RedaMohssine/E-Wslni-Autonomous-Guide-Robot/SolidWorks CAD/assem_moteur_roue.SLDASM

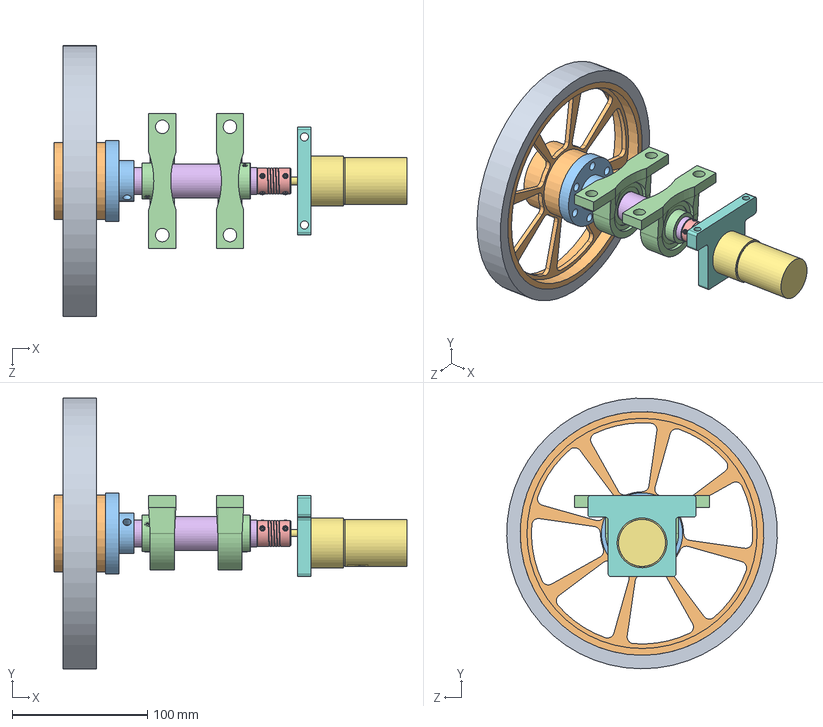
[picture p13: CAD file, 2026-05-02]
SolidWorks CAD/assem_moteur_roue.SLDASM
260.8 x 199.9 x 199.9 mm
fourche en T
moteur
arbre
Stepper Motor Flexible Coupling 6,35 x 8 mm
palier x 2
accouplement
