RedaMohssine/E-Wslni-Autonomous-Guide-Robot/SolidWorks CAD/Part1.SLDPRT

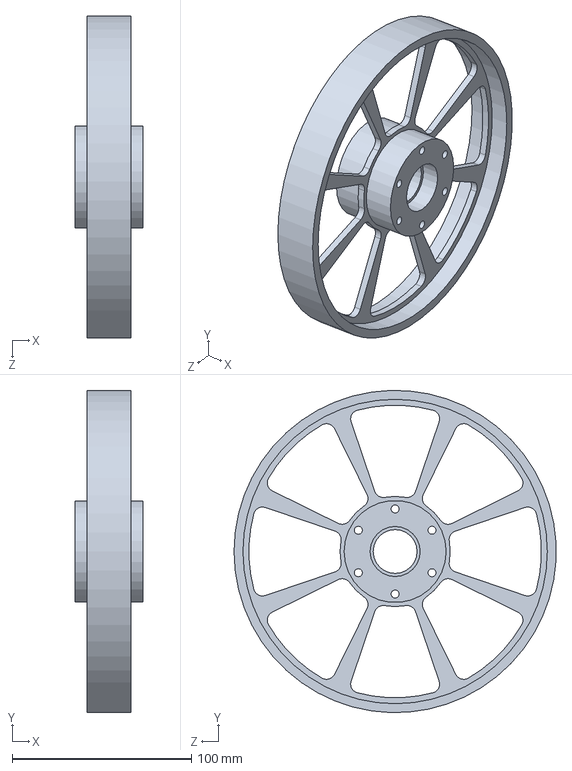
[picture p21: CAD file, 2026-05-02]
SolidWorks CAD/Part1.SLDPRT
38.0 x 179.9 x 179.8 mm
