RedaMohssine/E-Wslni-Autonomous-Guide-Robot/SolidWorks CAD/port male new.SLDPRT

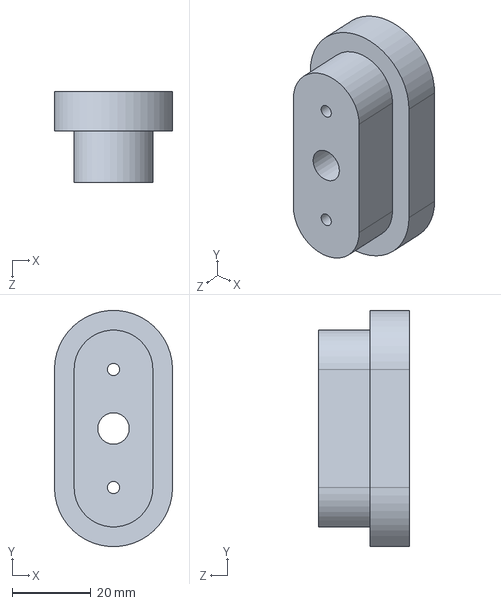
[picture p24: CAD file, 2026-05-02]
SolidWorks CAD/port male new.SLDPRT
30.0 x 59.9 x 23.0 mm
