RedaMohssine/E-Wslni-Autonomous-Guide-Robot/SolidWorks CAD/support  charge.SLDPRT

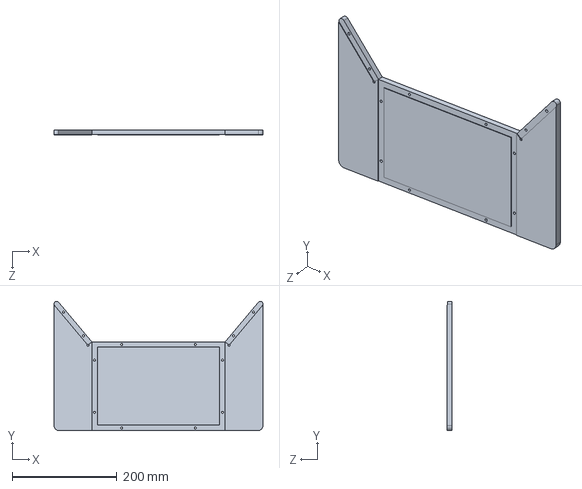
[picture p25: CAD file, 2026-05-02]
SolidWorks CAD/support charge.SLDPRT
400.0 x 247.6 x 10.0 mm
