RedaMohssine/E-Wslni-Autonomous-Guide-Robot/SolidWorks CAD/habillage_port_piece.SLDPRT

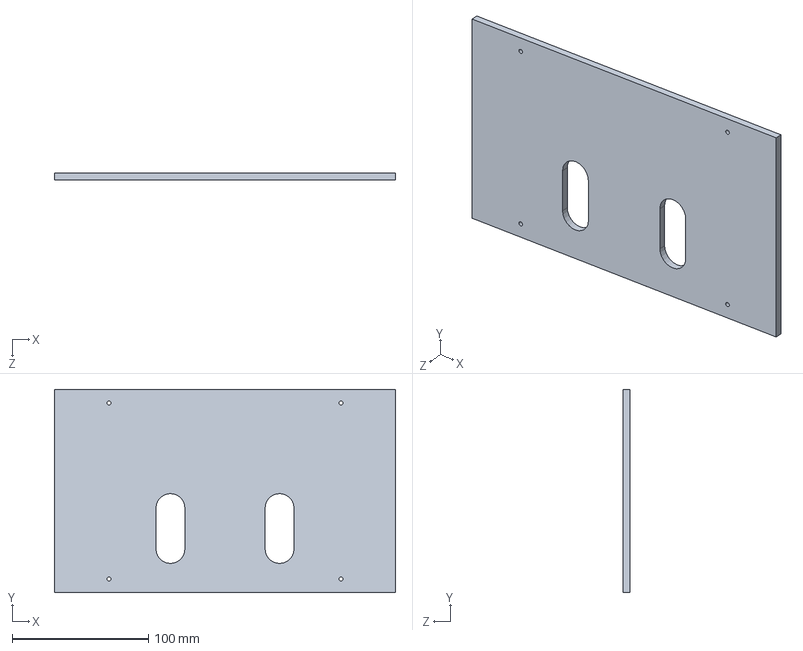
[picture p26: CAD file, 2026-05-02]
SolidWorks CAD/habillage_port_piece.SLDPRT
250.0 x 149.0 x 5.00 mm
