RedaMohssine/E-Wslni-Autonomous-Guide-Robot/SolidWorks CAD/roof.SLDPRT

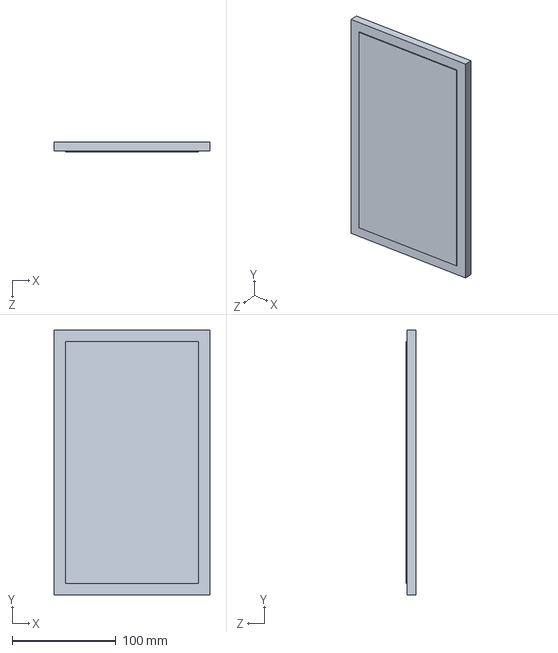
[picture p27: CAD file, 2026-05-02]
SolidWorks CAD/roof.SLDPRT
150.0 x 255.0 x 10.0 mm
