RedaMohssine/E-Wslni-Autonomous-Guide-Robot/SolidWorks CAD/lateral.SLDPRT

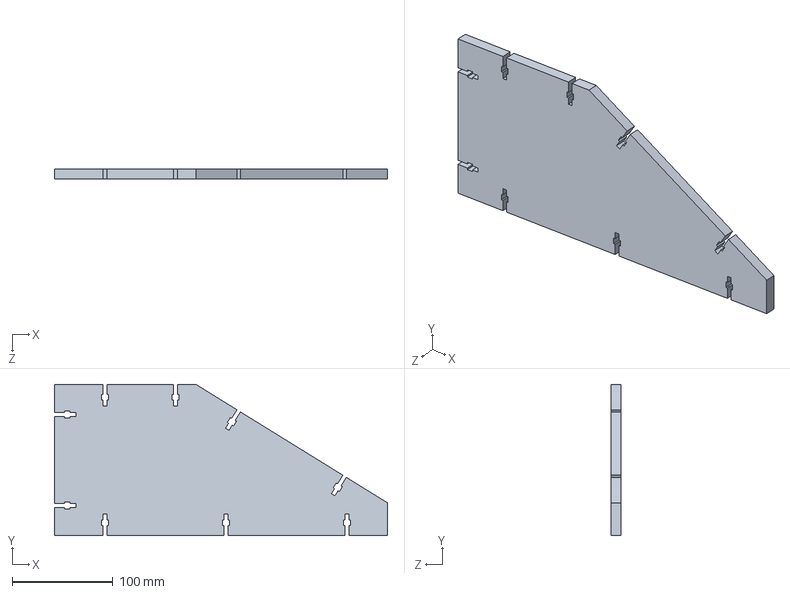
[picture p28: CAD file, 2026-05-02]
SolidWorks CAD/lateral.SLDPRT
330.0 x 150.0 x 10.0 mm
