RedaMohssine/E-Wslni-Autonomous-Guide-Robot/SolidWorks CAD/plateau4.SLDPRT

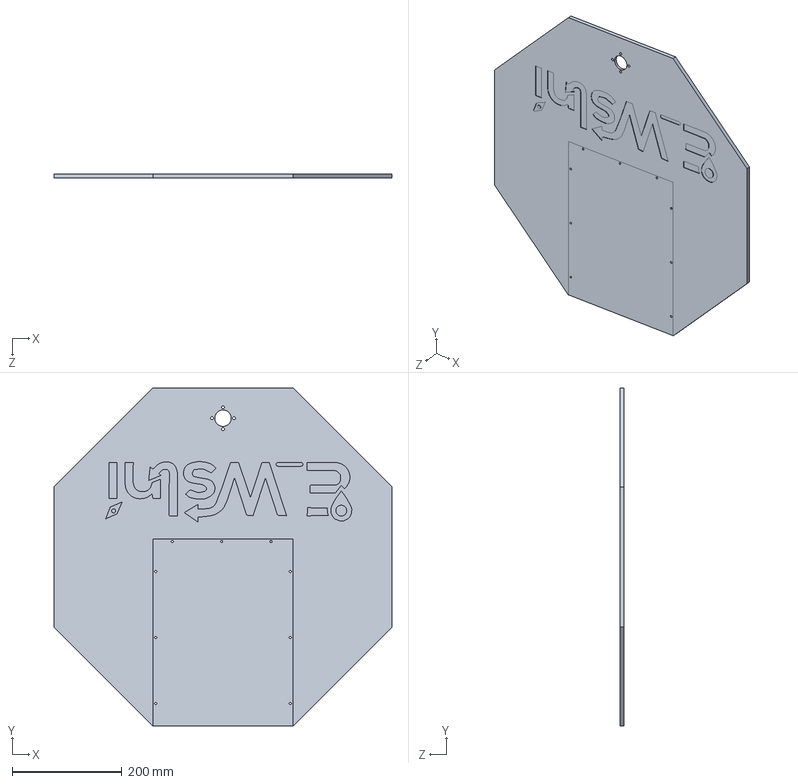
[picture p29: CAD file, 2026-05-02]
SolidWorks CAD/plateau4.SLDPRT
615.6 x 615.6 x 8.00 mm
