RedaMohssine/E-Wslni-Autonomous-Guide-Robot/SolidWorks CAD/paroi direction 1.SLDPRT

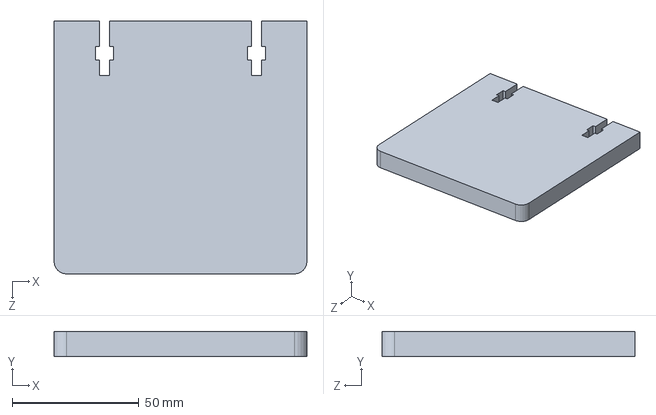
[picture p31: CAD file, 2026-05-02]
SolidWorks CAD/paroi direction 1.SLDPRT
100.0 x 10.0 x 100.0 mm
