RedaMohssine/E-Wslni-Autonomous-Guide-Robot/SolidWorks CAD/mount_bottom.SLDPRT

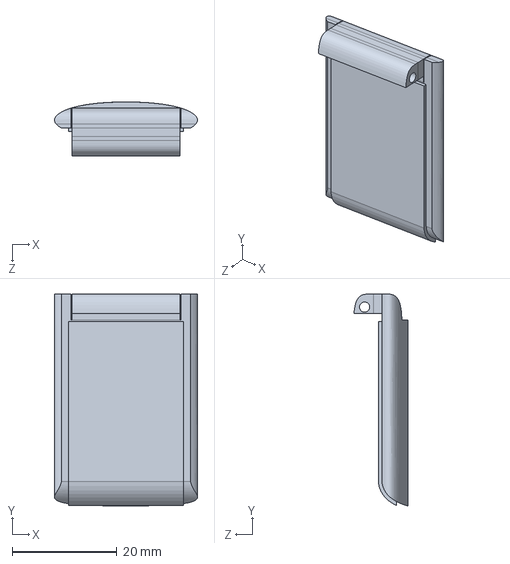
[picture p32: CAD file, 2026-05-02]
SolidWorks CAD/mount_bottom.SLDPRT
27.3 x 40.5 x 10.4 mm
