RedaMohssine/E-Wslni-Autonomous-Guide-Robot/SolidWorks CAD/RUBBER WHEEL (2.5inch).SLDPRT

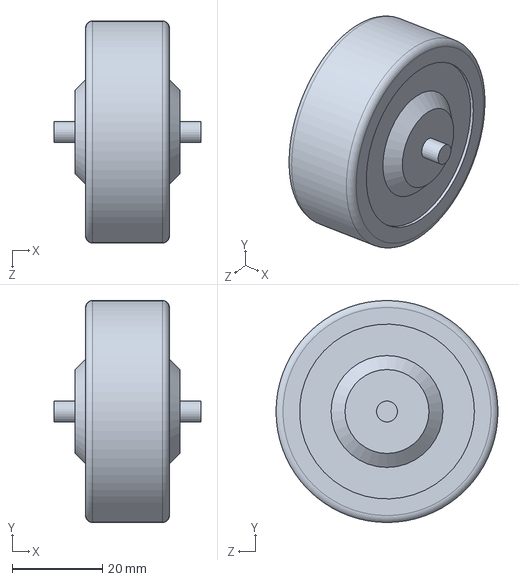
[picture p33: CAD file, 2026-05-02]
SolidWorks CAD/RUBBER WHEEL (2.5inch).SLDPRT
32.6 x 49.3 x 49.3 mm
