RedaMohssine/E-Wslni-Autonomous-Guide-Robot/SolidWorks CAD/supp_moteur.SLDPRT

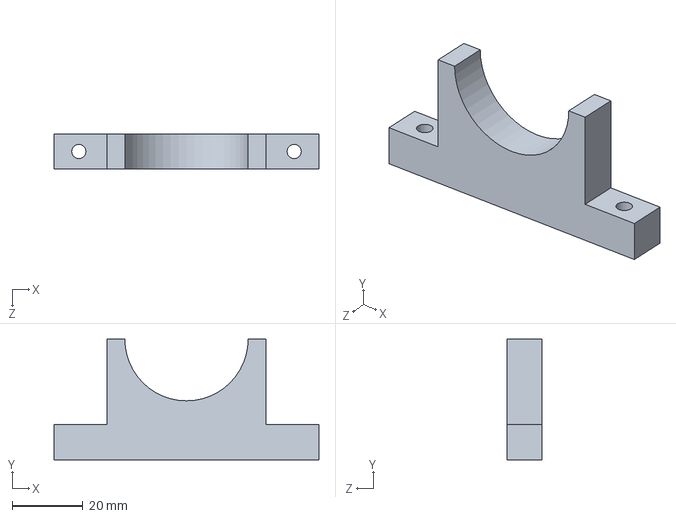
[picture p34: CAD file, 2026-05-02]
SolidWorks CAD/supp_moteur.SLDPRT
74.8 x 34.2 x 10.0 mm
