RedaMohssine/E-Wslni-Autonomous-Guide-Robot/SolidWorks CAD/CASTER WHEEL BASE LOCK.SLDPRT

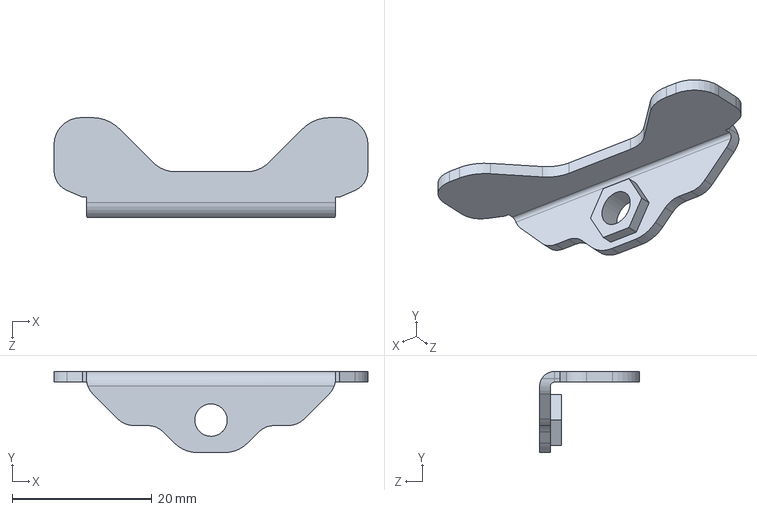
[picture p35: CAD file, 2026-05-02]
SolidWorks CAD/CASTER WHEEL BASE LOCK.SLDPRT
45.0 x 11.6 x 14.3 mm
