RedaMohssine/E-Wslni-Autonomous-Guide-Robot/SolidWorks CAD/Arduino Mega 2560.step

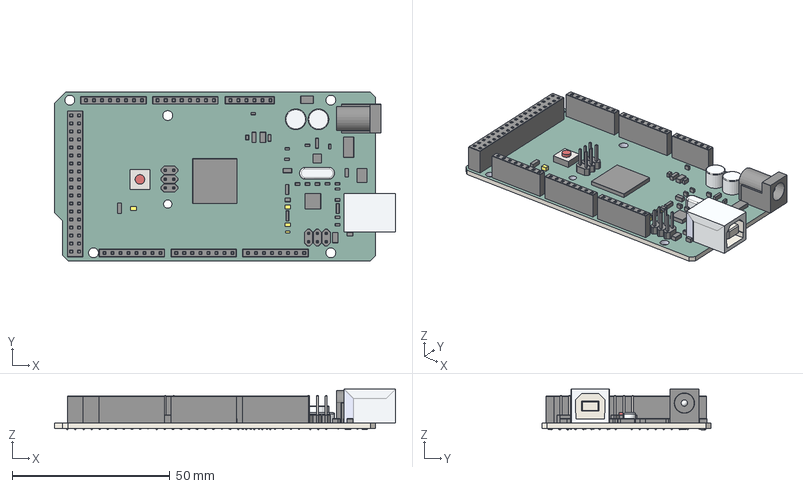
[picture p36: CAD file, 2026-05-02]
SolidWorks CAD/Arduino Mega 2560.step
107.9 x 53.4 x 13.0 mm
