RedaMohssine/E-Wslni-Autonomous-Guide-Robot/SolidWorks CAD/SD161.SLDPRT

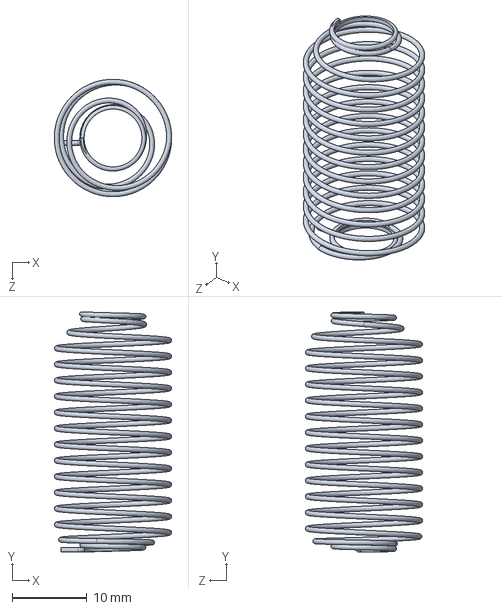
[picture p37: CAD file, 2026-05-02]
SolidWorks CAD/SD161.SLDPRT
15.7 x 32.1 x 15.7 mm
