RedaMohssine/E-Wslni-Autonomous-Guide-Robot/SolidWorks CAD/arbre.SLDPRT

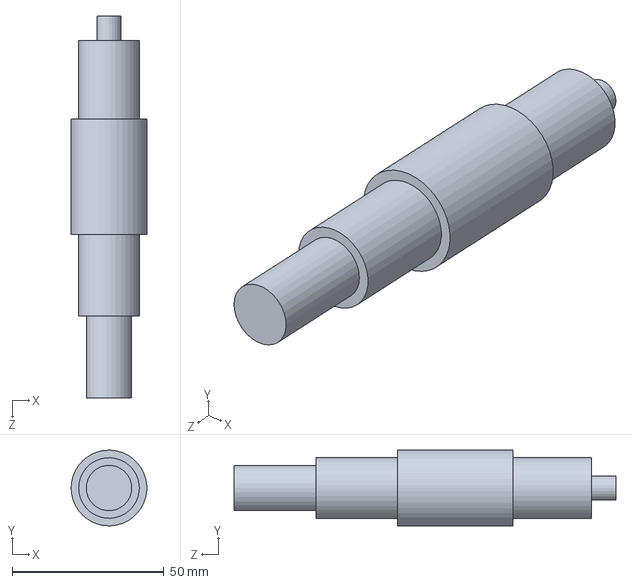
[picture p38: CAD file, 2026-05-02]
SolidWorks CAD/arbre.SLDPRT
25.0 x 25.0 x 126.0 mm
