RedaMohssine/E-Wslni-Autonomous-Guide-Robot/SolidWorks CAD/m920.step

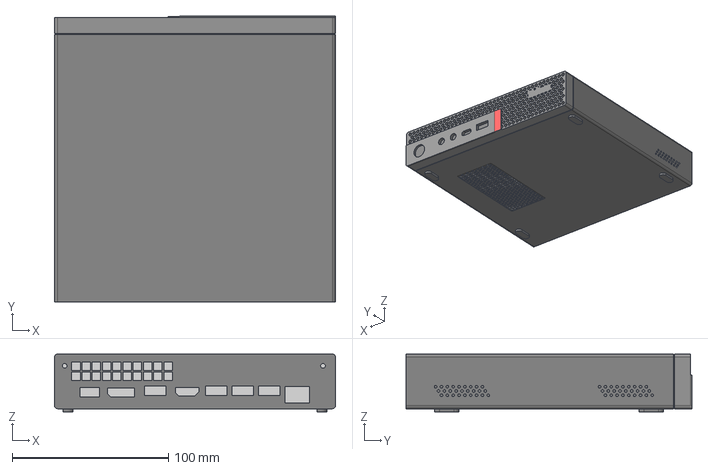
[picture p39: CAD file, 2026-05-02]
SolidWorks CAD/m920.step
180.0 x 183.0 x 37.0 mm
