RedaMohssine/E-Wslni-Autonomous-Guide-Robot/SolidWorks CAD/Port_male.SLDPRT

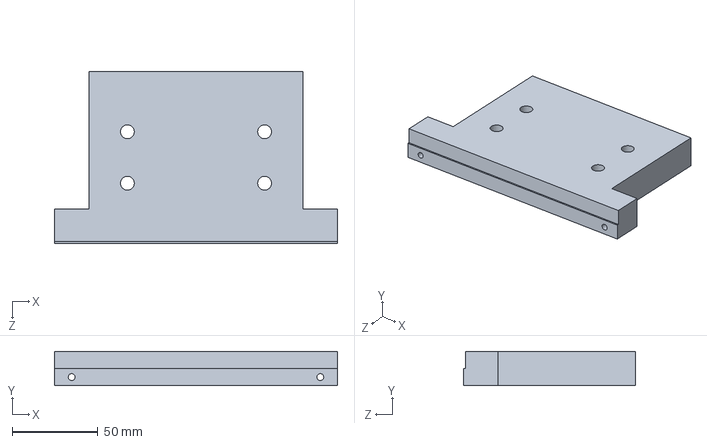
[picture p40: CAD file, 2026-05-02]
SolidWorks CAD/Port_male.SLDPRT
165.0 x 20.0 x 100.0 mm
