RedaMohssine/E-Wslni-Autonomous-Guide-Robot/SolidWorks CAD/front.SLDPRT

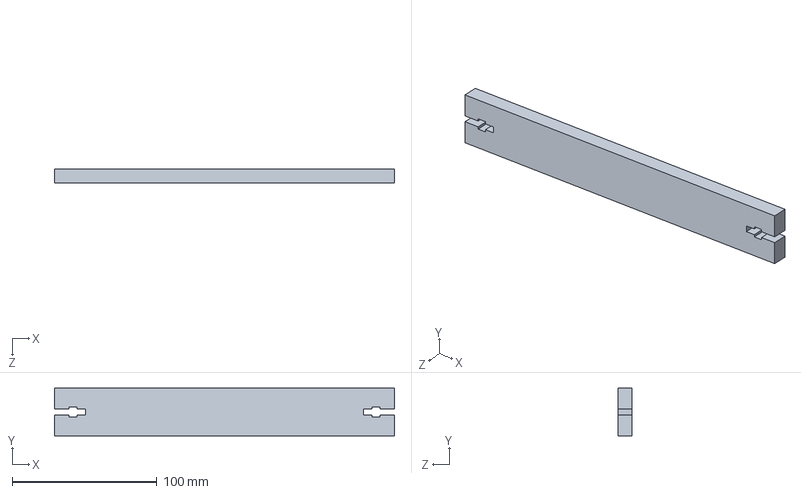
[picture p41: CAD file, 2026-05-02]
SolidWorks CAD/front.SLDPRT
235.0 x 33.0 x 10.0 mm
