RedaMohssine/E-Wslni-Autonomous-Guide-Robot/SolidWorks CAD/Stepper Motor Flexible Coupling 6,35 x 8 mm.SLDPRT

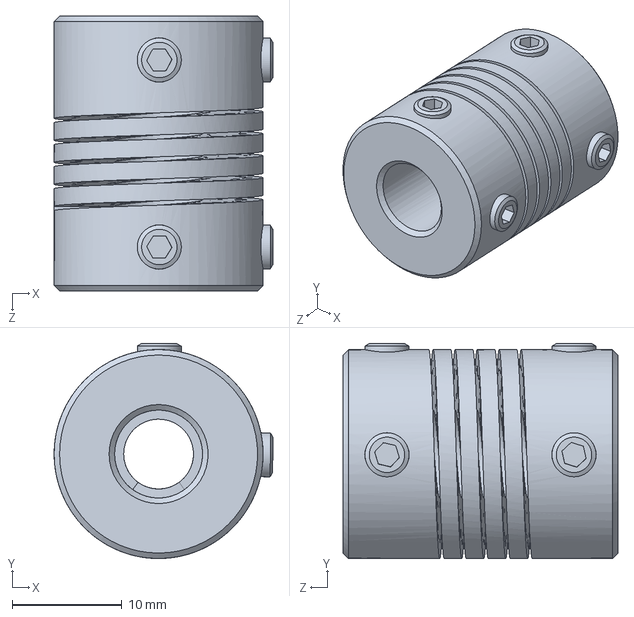
[picture p42: CAD file, 2026-05-02]
SolidWorks CAD/Stepper Motor Flexible Coupling 6,35 x 8 mm.SLDPRT
19.9 x 19.6 x 25.0 mm
