RedaMohssine/E-Wslni-Autonomous-Guide-Robot/SolidWorks CAD/Part2.SLDPRT

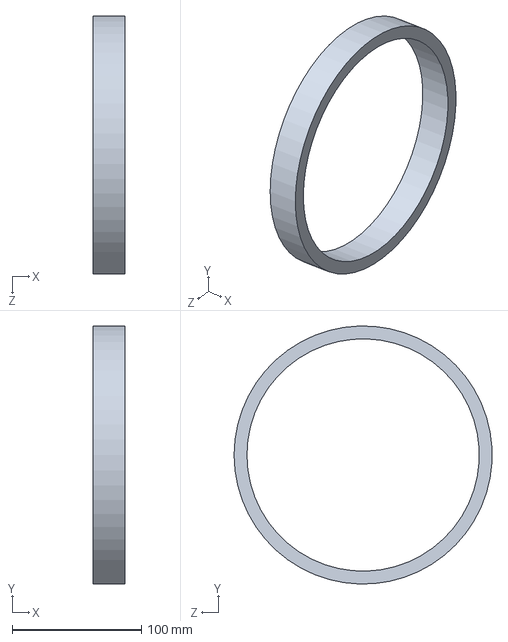
[picture p43: CAD file, 2026-05-02]
SolidWorks CAD/Part2.SLDPRT
24.5 x 199.9 x 199.8 mm
