RedaMohssine/E-Wslni-Autonomous-Guide-Robot/SolidWorks CAD/base.SLDPRT

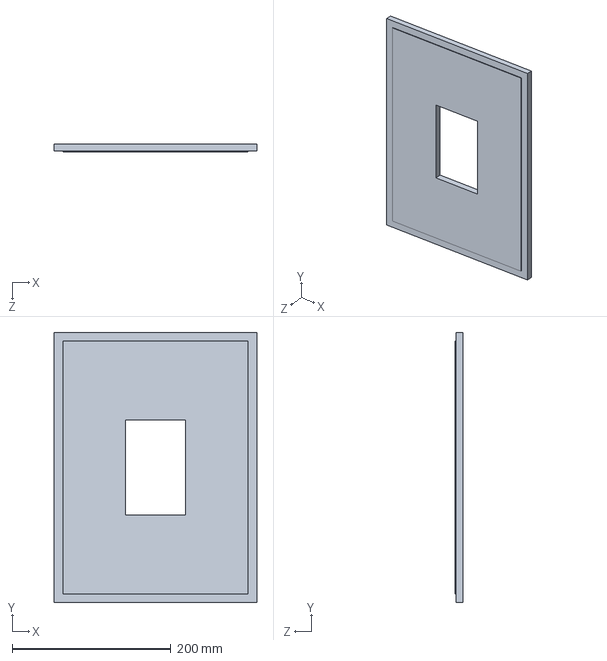
[picture p44: CAD file, 2026-05-02]
SolidWorks CAD/base.SLDPRT
255.0 x 340.0 x 10.0 mm
