RedaMohssine/E-Wslni-Autonomous-Guide-Robot/SolidWorks CAD/Vis_guide.SLDPRT

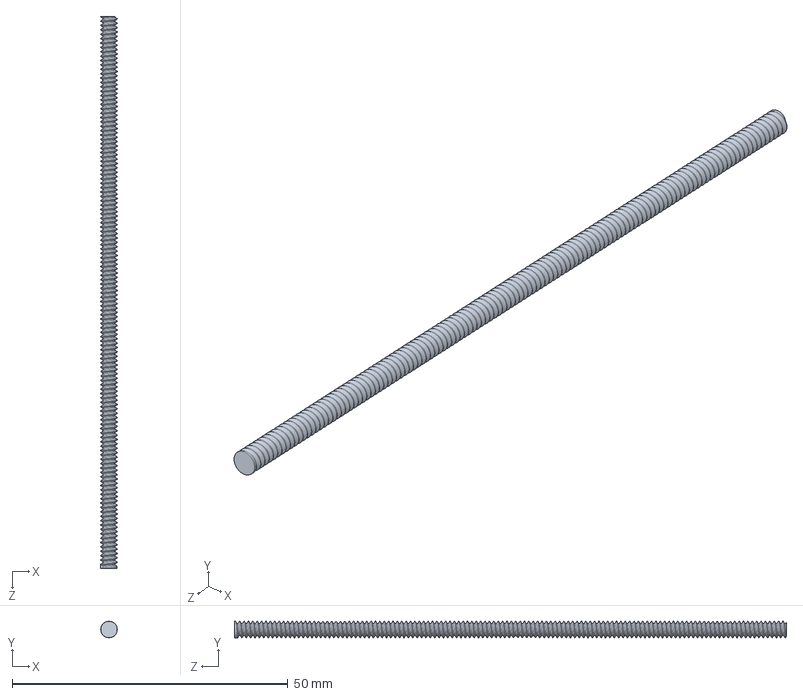
[picture p45: CAD file, 2026-05-02]
SolidWorks CAD/Vis_guide.SLDPRT
3.00 x 3.00 x 100.0 mm
