RedaMohssine/E-Wslni-Autonomous-Guide-Robot/SolidWorks CAD/plateau3.SLDPRT

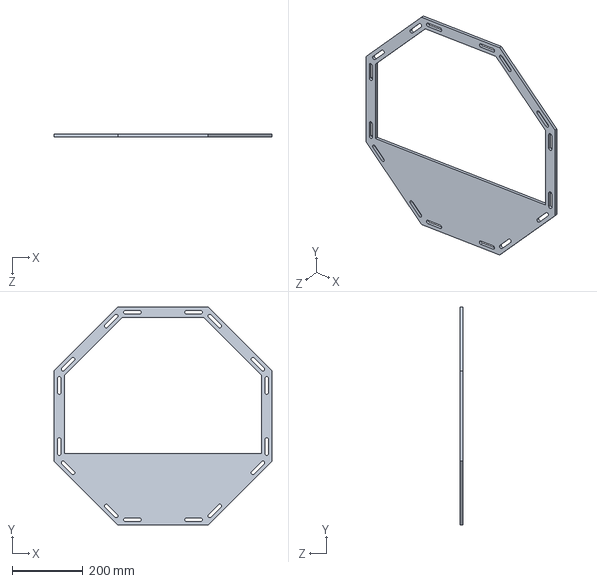
[picture p46: CAD file, 2026-05-02]
SolidWorks CAD/plateau3.SLDPRT
615.6 x 615.6 x 8.00 mm
