RedaMohssine/E-Wslni-Autonomous-Guide-Robot/SolidWorks CAD/palier.SLDPRT

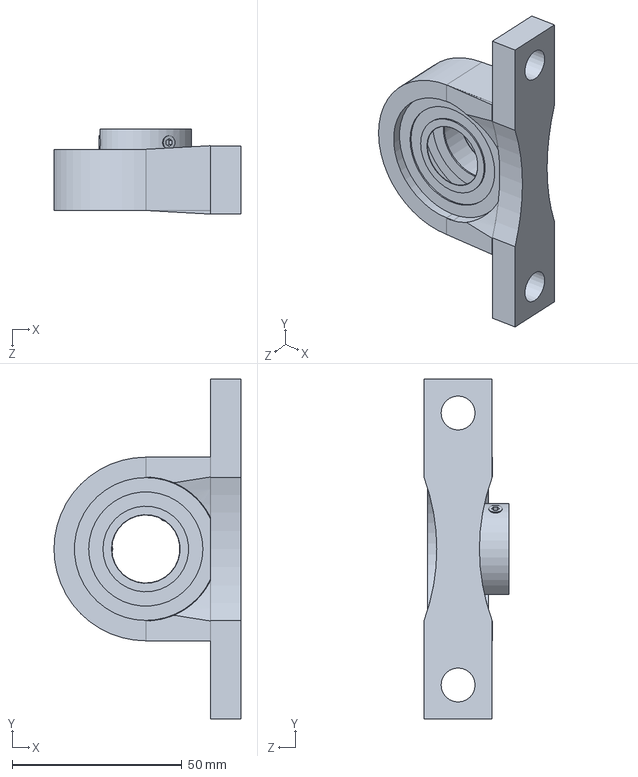
[picture p47: CAD file, 2026-05-02]
SolidWorks CAD/palier.SLDPRT
55.0 x 100.0 x 25.1 mm
