RedaMohssine/E-Wslni-Autonomous-Guide-Robot/SolidWorks CAD/back.SLDPRT

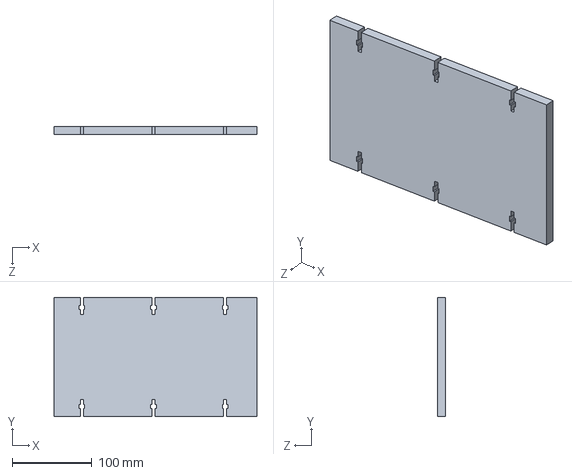
[picture p48: CAD file, 2026-05-02]
SolidWorks CAD/back.SLDPRT
255.0 x 150.0 x 10.0 mm
