RedaMohssine/E-Wslni-Autonomous-Guide-Robot/SolidWorks CAD/batterie_Turnigy.SLDPRT

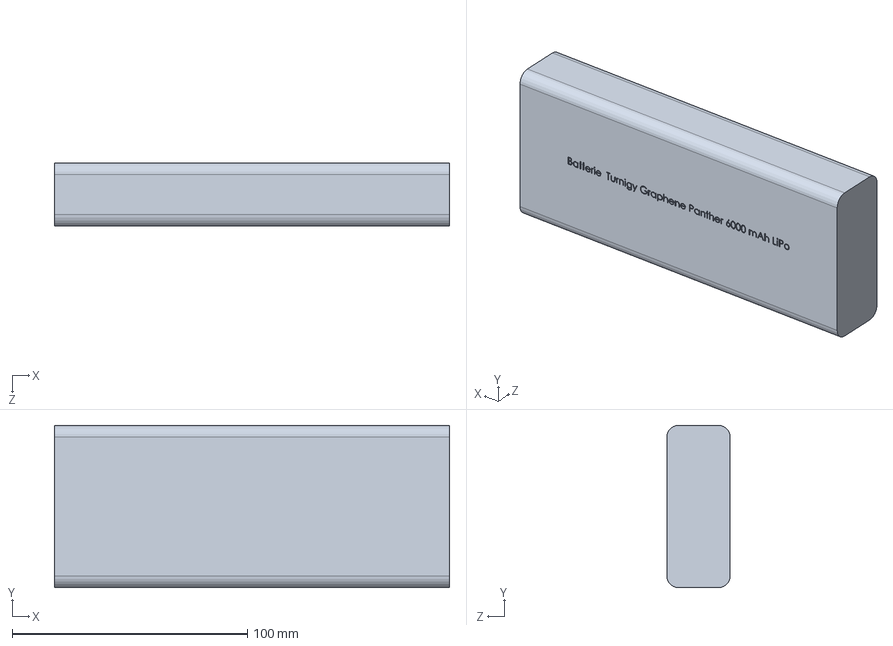
[picture p49: CAD file, 2026-05-02]
SolidWorks CAD/batterie_Turnigy.SLDPRT
168.0 x 69.0 x 27.0 mm
