RedaMohssine/E-Wslni-Autonomous-Guide-Robot/SolidWorks CAD/moteur.SLDPRT

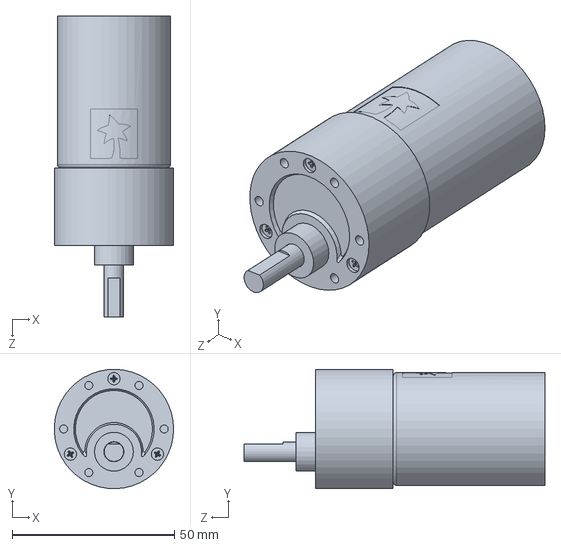
[picture p50: CAD file, 2026-05-02]
SolidWorks CAD/moteur.SLDPRT
36.8 x 36.8 x 92.8 mm
