RedaMohssine/E-Wslni-Autonomous-Guide-Robot/SolidWorks CAD/chassis_v2.SLDPRT

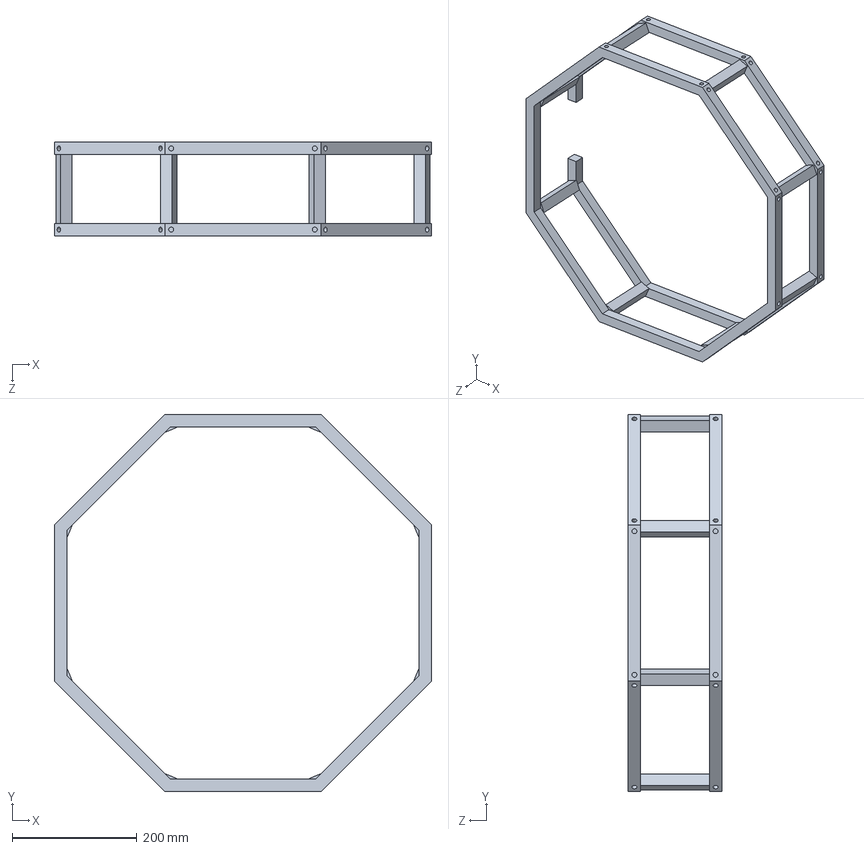
[picture p51: CAD file, 2026-05-02]
SolidWorks CAD/chassis_v2.SLDPRT
603.6 x 603.6 x 150.0 mm
