RedaMohssine/E-Wslni-Autonomous-Guide-Robot/SolidWorks CAD/fourche en T.SLDPRT

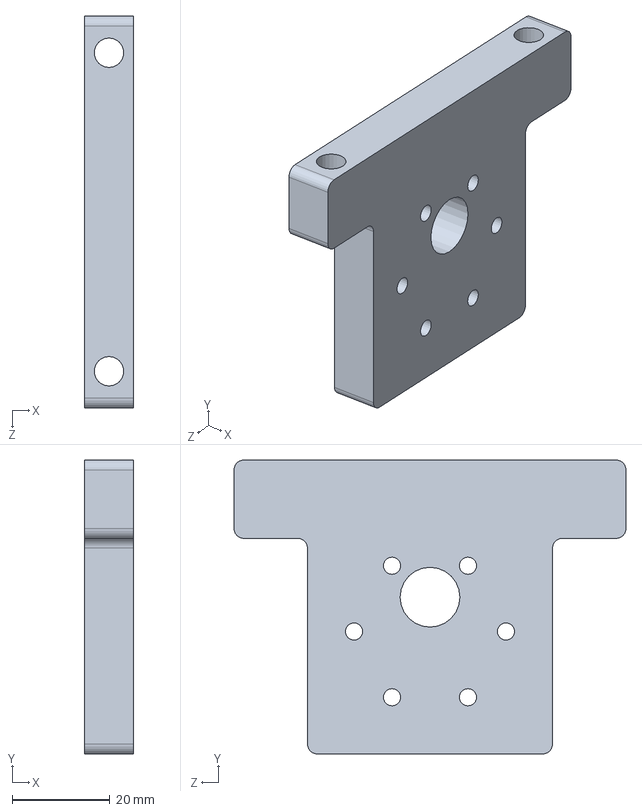
[picture p52: CAD file, 2026-05-02]
SolidWorks CAD/fourche en T.SLDPRT
10.0 x 60.0 x 80.0 mm
