RedaMohssine/E-Wslni-Autonomous-Guide-Robot/SolidWorks CAD/CASTER WHEEL BASE.SLDPRT

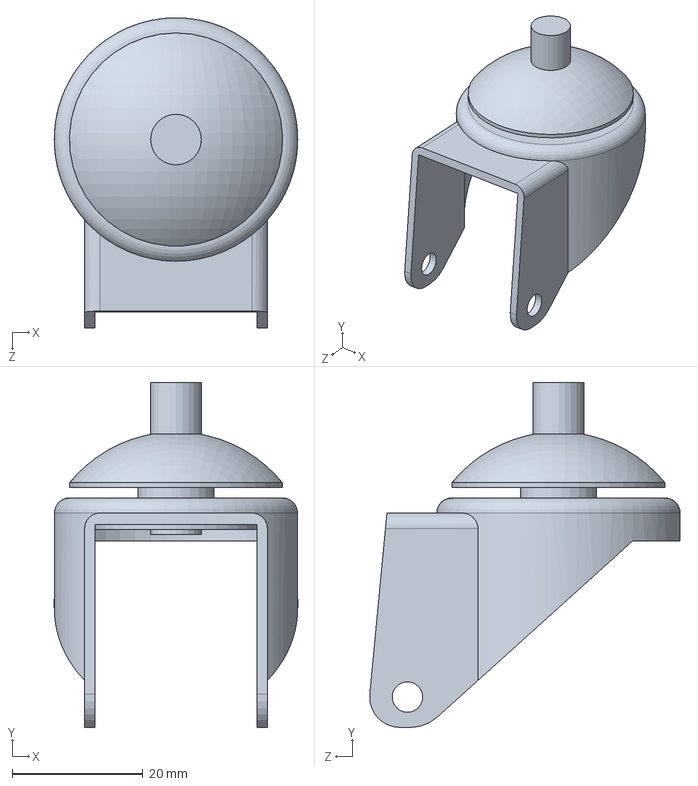
[picture p53: CAD file, 2026-05-02]
SolidWorks CAD/CASTER WHEEL BASE.SLDPRT
37.3 x 52.8 x 47.5 mm
