RedaMohssine/E-Wslni-Autonomous-Guide-Robot/SolidWorks CAD/accouplement.SLDPRT

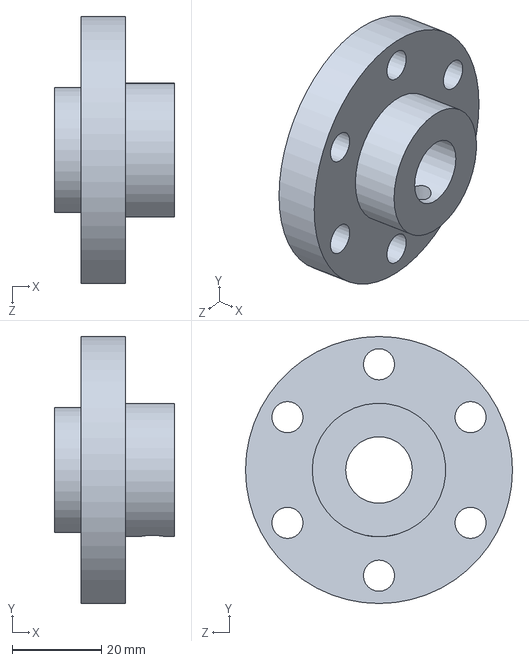
[picture p54: CAD file, 2026-05-02]
SolidWorks CAD/accouplement.SLDPRT
27.0 x 60.0 x 60.0 mm
