RedaMohssine/E-Wslni-Autonomous-Guide-Robot/SolidWorks CAD/supportcamera.SLDPRT

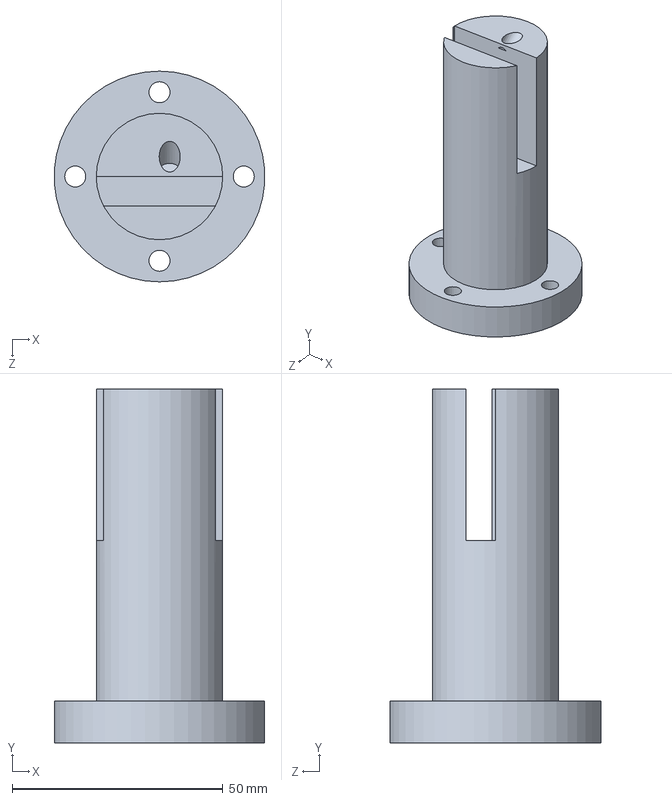
[picture p55: CAD file, 2026-05-02]
SolidWorks CAD/supportcamera.SLDPRT
49.9 x 84.0 x 50.0 mm
