RedaMohssine/E-Wslni-Autonomous-Guide-Robot/SolidWorks CAD/plateau1.SLDPRT

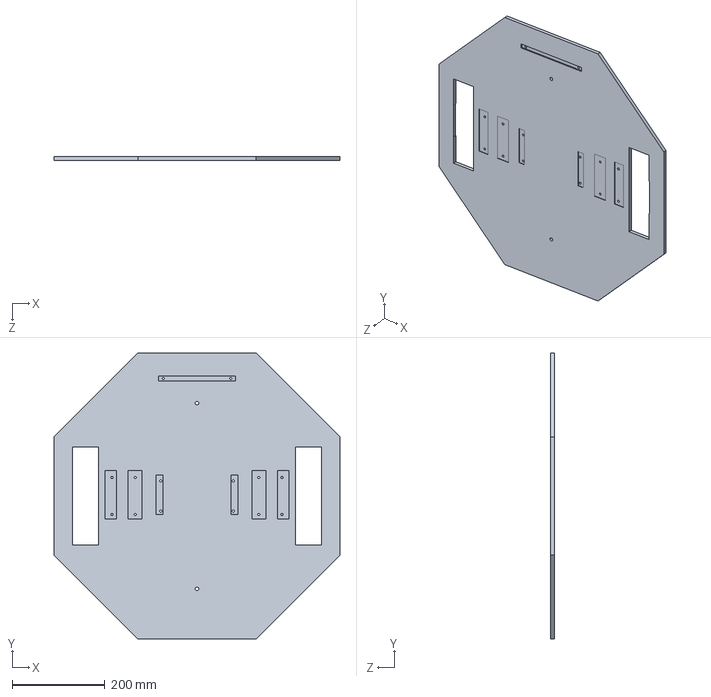
[picture p56: CAD file, 2026-05-02]
SolidWorks CAD/plateau1.SLDPRT
615.6 x 615.6 x 8.00 mm
