RedaMohssine/E-Wslni-Autonomous-Guide-Robot/SolidWorks CAD/interface.SLDPRT

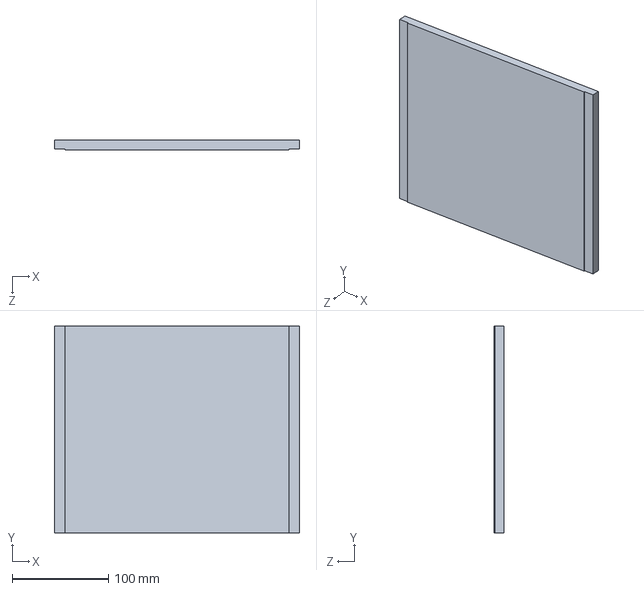
[picture p57: CAD file, 2026-05-02]
SolidWorks CAD/interface.SLDPRT
255.0 x 215.0 x 10.0 mm
