RedaMohssine/E-Wslni-Autonomous-Guide-Robot/SolidWorks CAD/plaque conductrice port male.SLDPRT

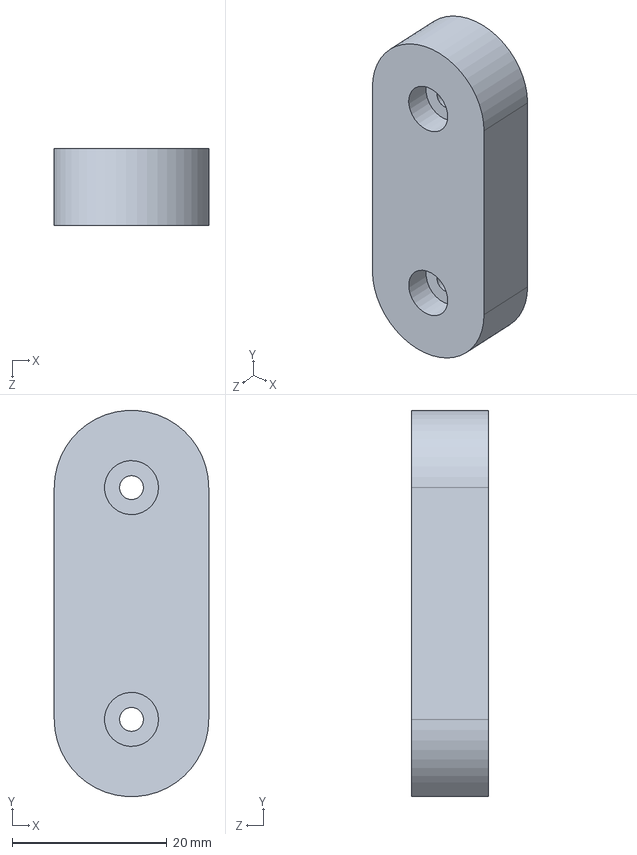
[picture p58: CAD file, 2026-05-02]
SolidWorks CAD/plaque conductrice port male.SLDPRT
20.0 x 50.0 x 10.0 mm
