RedaMohssine/E-Wslni-Autonomous-Guide-Robot/SolidWorks CAD/mur 1.SLDPRT

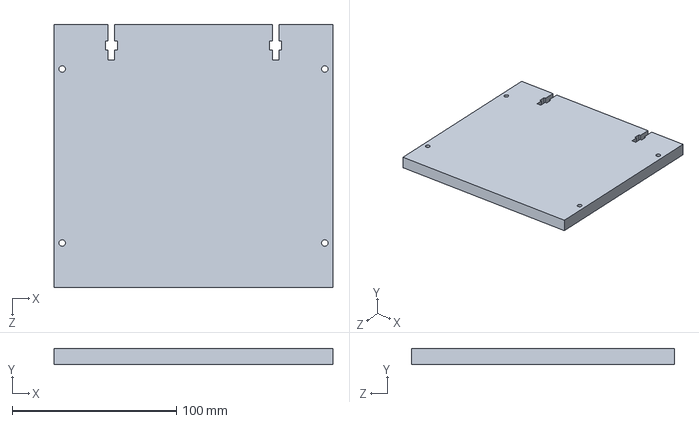
[picture p59: CAD file, 2026-05-02]
SolidWorks CAD/mur 1.SLDPRT
170.0 x 10.0 x 160.0 mm
