RedaMohssine/E-Wslni-Autonomous-Guide-Robot/SolidWorks CAD/LCD 7 inch.SLDASM

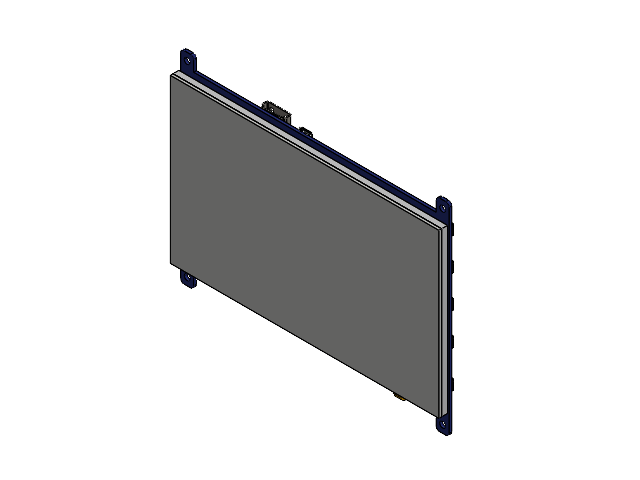
[picture p60: CAD file, 2026-05-02]
SolidWorks CAD/LCD 7 inch.SLDASM
shield.step
socket_housing.step
socket_plate.step
terminal.step x 5
26-Pin-Header-Female-Double-2.54mm.step
molex_0471510001.step
Tactal Switch - SMD (6mmx 6mmx 5mm) - Marked.step x 5
zl202-26_p2-54_l33-0_w5-08_h8-9.step
LCD 7 inch_1.step
LCD 7 inch-0.step
LCD 7 inch-1.step
LCD 7 inch-2.step
LCD 7 inch-3.step
LCD 7 inch-4.step
